vacergvo/BE_AIME/Spice/AIME_2.asc

C1: cap; 1n
C2: cap; 1µ
C3: cap; 100n
C4: cap; 100n
C5: cap; 1p
I1: current; PULSE(50n 100n 1 0.1 0.1 2); AC 1
R1: res; 10k
R2: res; 100k
R3: res; 1k
R4: res; 100k
R5: res; 1k
U1: LTC1050
V1: voltage; 5
V2: voltage; SINE(0 325 50)
Named nets: 0
ADC
.tran 4
.ac dec 100 1 1G
