vacergvo/BE_AIME/Spice/AIME_3.asc

C1: cap; 1n
C2: cap; 1µ
C3: cap; 100n
C4: cap; 100n
C5: cap; 1p
R1: res; 10k
R2: res; 100k
R3: res; 1k
R4: res; 100k
R5: res; 1k
U1: LTC1050
V1: voltage; 5
V2: voltage; SINE(0 325 50); AC 1
V3: voltage; PULSE(0 1 0.2 0.1 0.1 1)
X1: S_AIME
Named nets: 0
ADC
.tran 4
.ac dec 100 1 1G
.param R1=1k
.param C1=200u
