vacergvo/BE_AIME/Spice/S_AIME.asc

B1: bi; I=v(cp,cn)*(10n+10n*v(gc,gn))
C1: cap; {C1}
R1: res; {R1}
Named nets: gp, gn, gc, cp, cn
